Lambdacorporation/Seminarni_prace_Dvorak_2023/src/obrázky/500x500 bez můstků-1_1.jpg

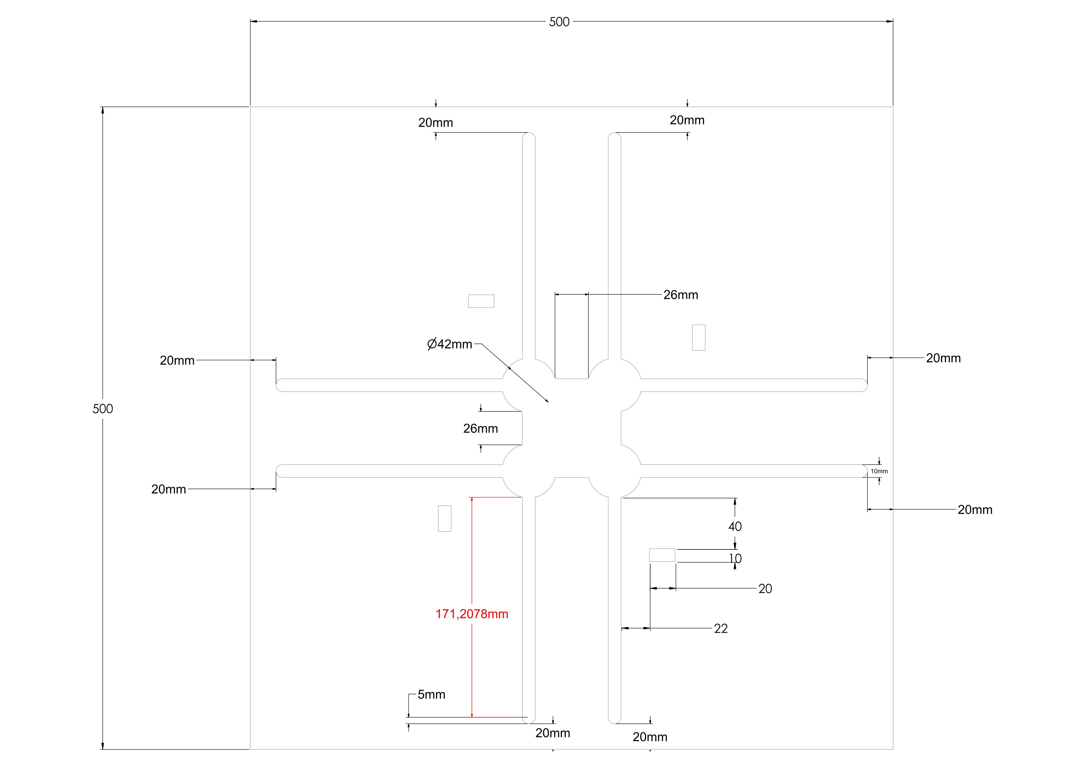
src/obrázky/500x500 bez můstků-1_1.jpg
