Lambdacorporation/Seminarni_prace_Dvorak_2023/src/obrázky/500x500 výpalek + zbytky.jpg

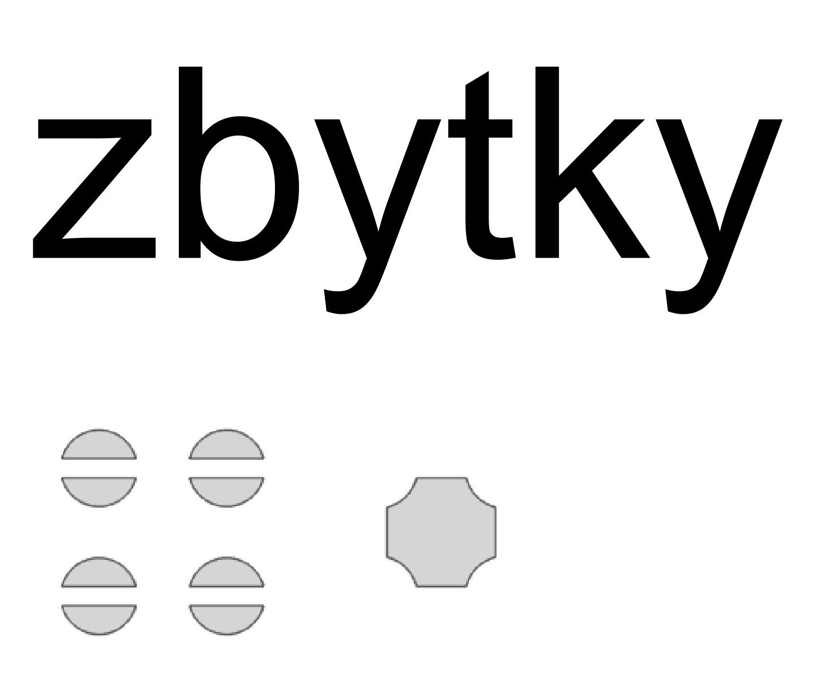
src/obrázky/500x500 výpalek + zbytky.jpg
