Lambdacorporation/Seminarni_prace_Dvorak_2023/src/obrázky/500x500 výpalek + zbytky_1.jpg

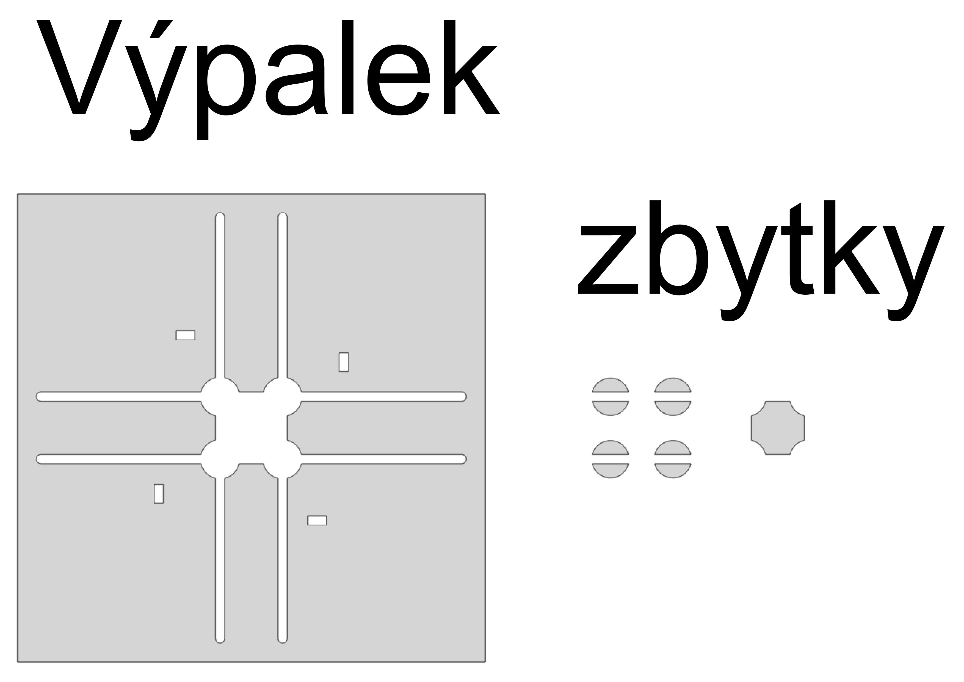
src/obrázky/500x500 výpalek + zbytky_1.jpg
