Lambdacorporation/Seminarni_prace_Dvorak_2023/src/obrázky/bok.png

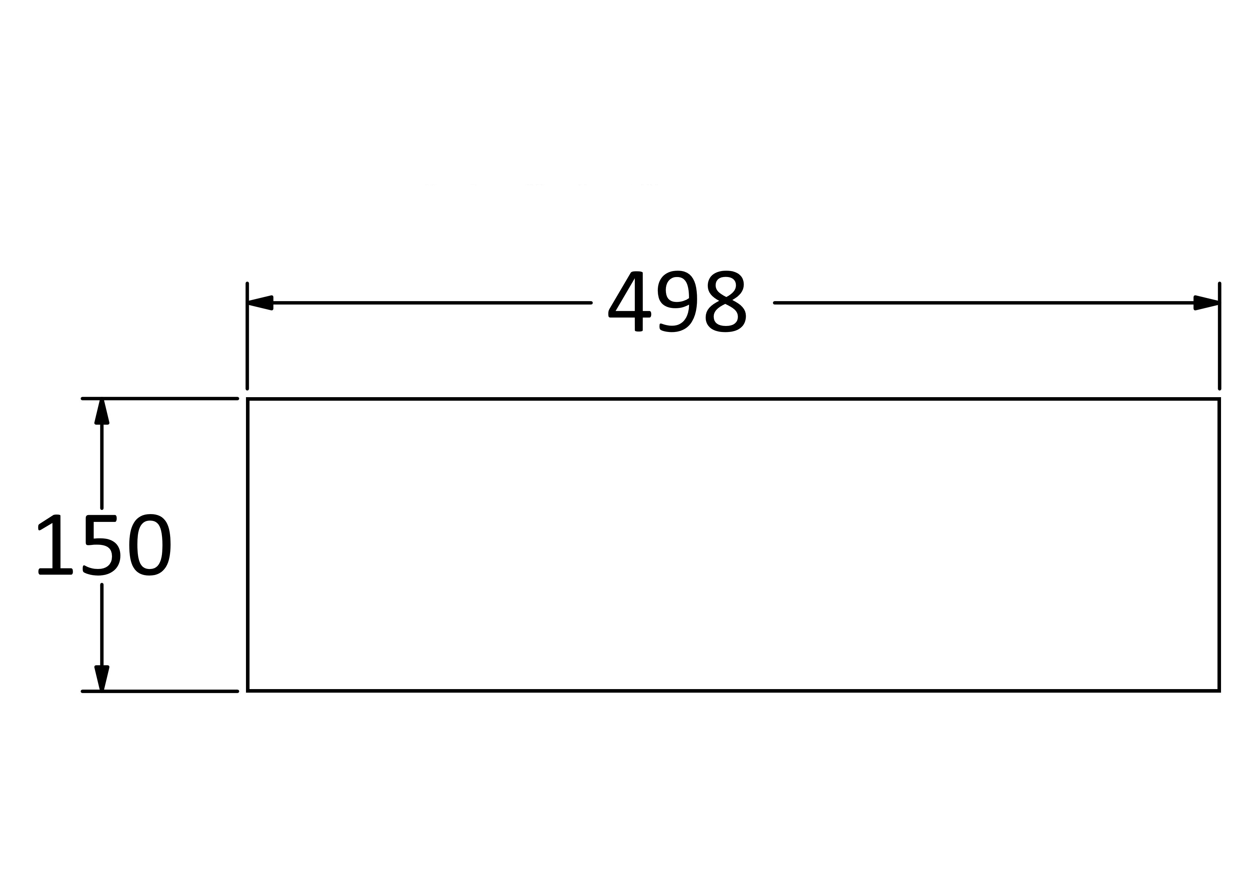
src/obrázky/bok.png
