Lambdacorporation/Seminarni_prace_Dvorak_2023/src/obrázky/boční stěna 2x_1.jpg

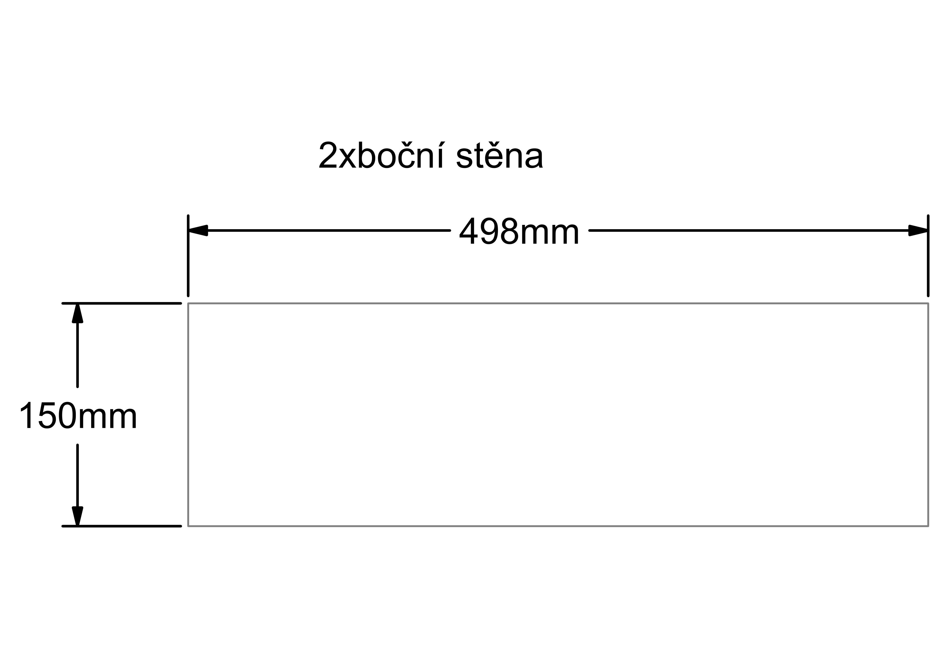
src/obrázky/boční stěna 2x_1.jpg
