Lambdacorporation/Seminarni_prace_Dvorak_2023/src/obrázky/dno 1x_1.jpg

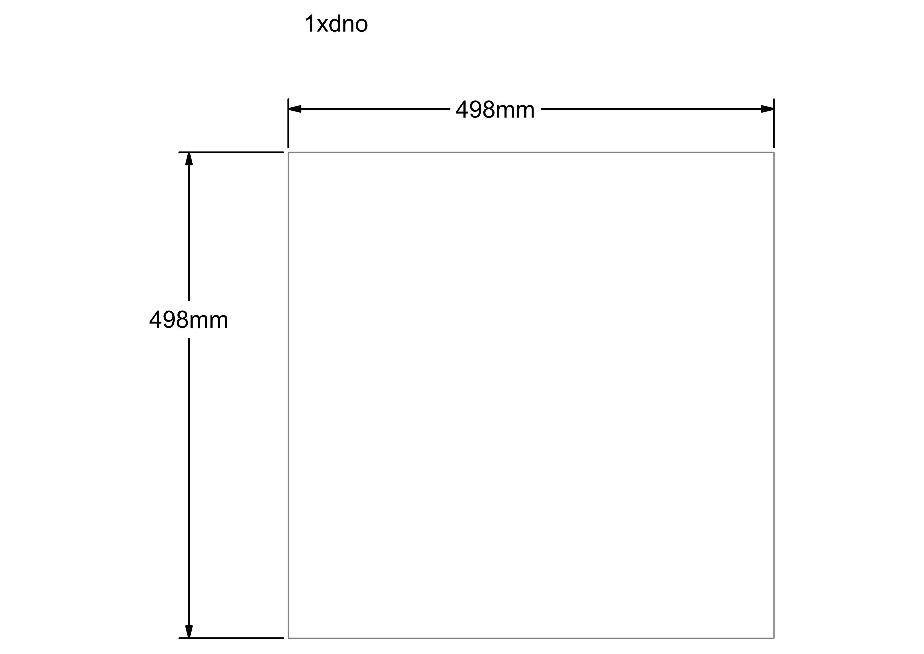
src/obrázky/dno 1x_1.jpg
