Lambdacorporation/Seminarni_prace_Dvorak_2023/src/obrázky/dno.png

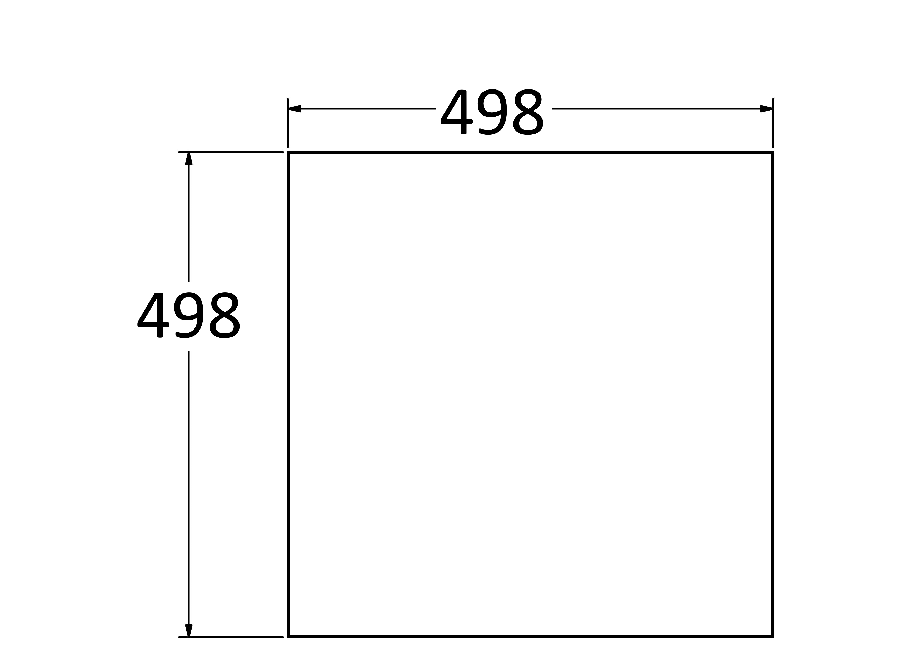
src/obrázky/dno.png
