Lambdacorporation/Seminarni_prace_Dvorak_2023/src/obrázky/krizovatky/dpv.bmp

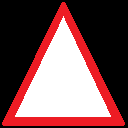
src/obrázky/krizovatky/dpv.bmp
