Lambdacorporation/Seminarni_prace_Dvorak_2023/src/obrázky/krizovatky/hpk.bmp

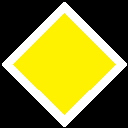
src/obrázky/krizovatky/hpk.bmp
