Lambdacorporation/Seminarni_prace_Dvorak_2023/src/obrázky/krizovatky/krizovatka6.jpg

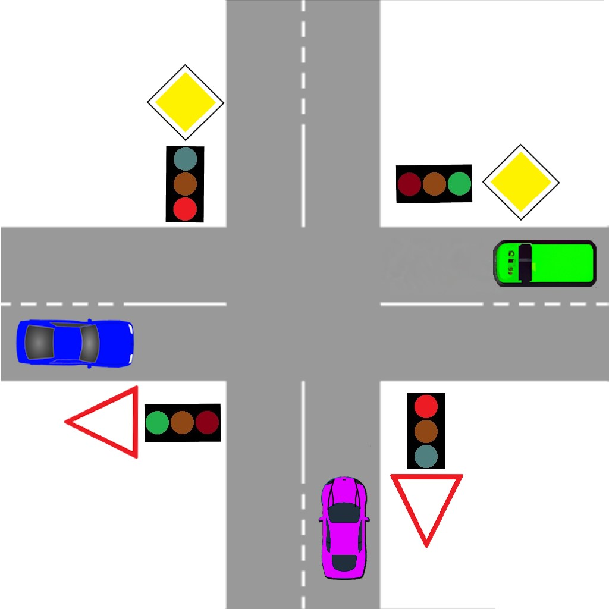
src/obrázky/krizovatky/krizovatka6.jpg
