Lambdacorporation/Seminarni_prace_Dvorak_2023/src/obrázky/krizovatky/krizovatka.png

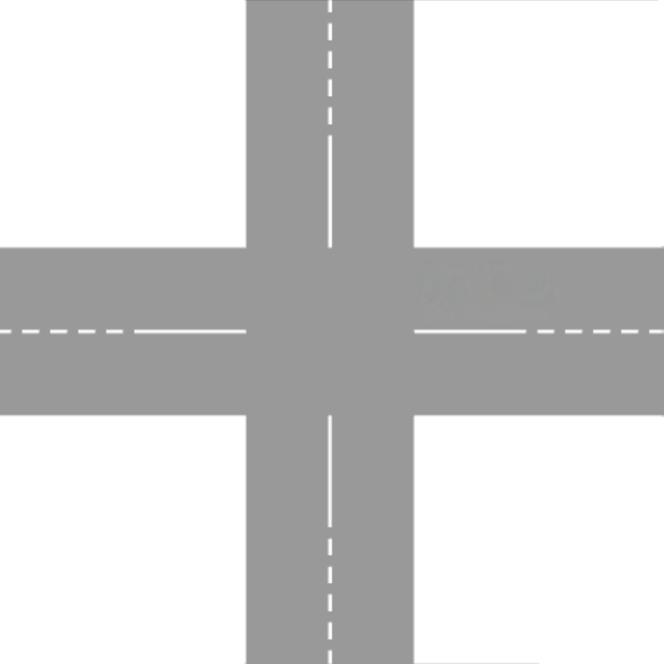
src/obrázky/krizovatky/krizovatka.png
