Lambdacorporation/Seminarni_prace_Dvorak_2023/src/obrázky/krizovatky/modre_auto.png

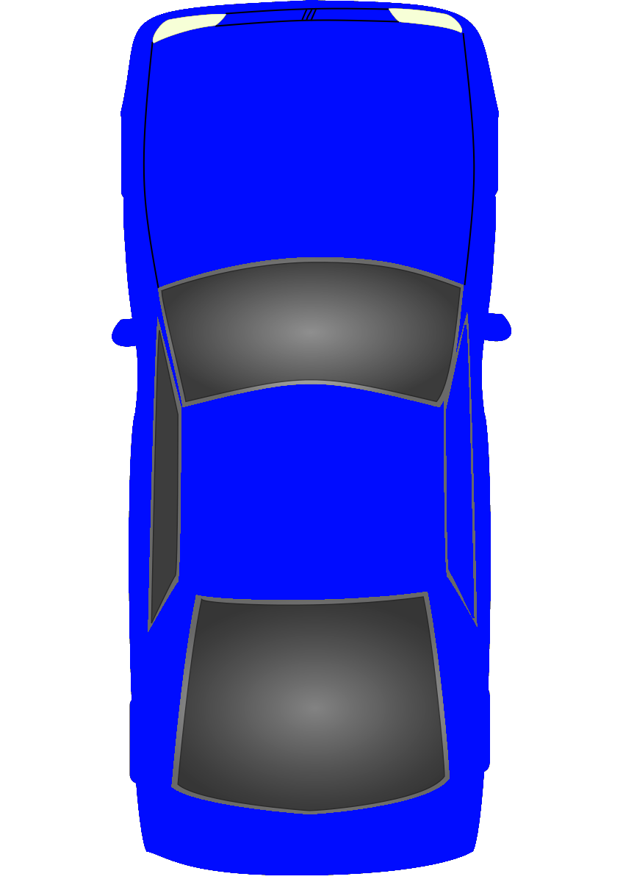
src/obrázky/krizovatky/modre_auto.png
