Lambdacorporation/Seminarni_prace_Dvorak_2023/src/obrázky/krizovatky/stop.png

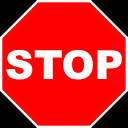
src/obrázky/krizovatky/stop.png
