Lambdacorporation/Seminarni_prace_Dvorak_2023/src/obrázky/předek.png

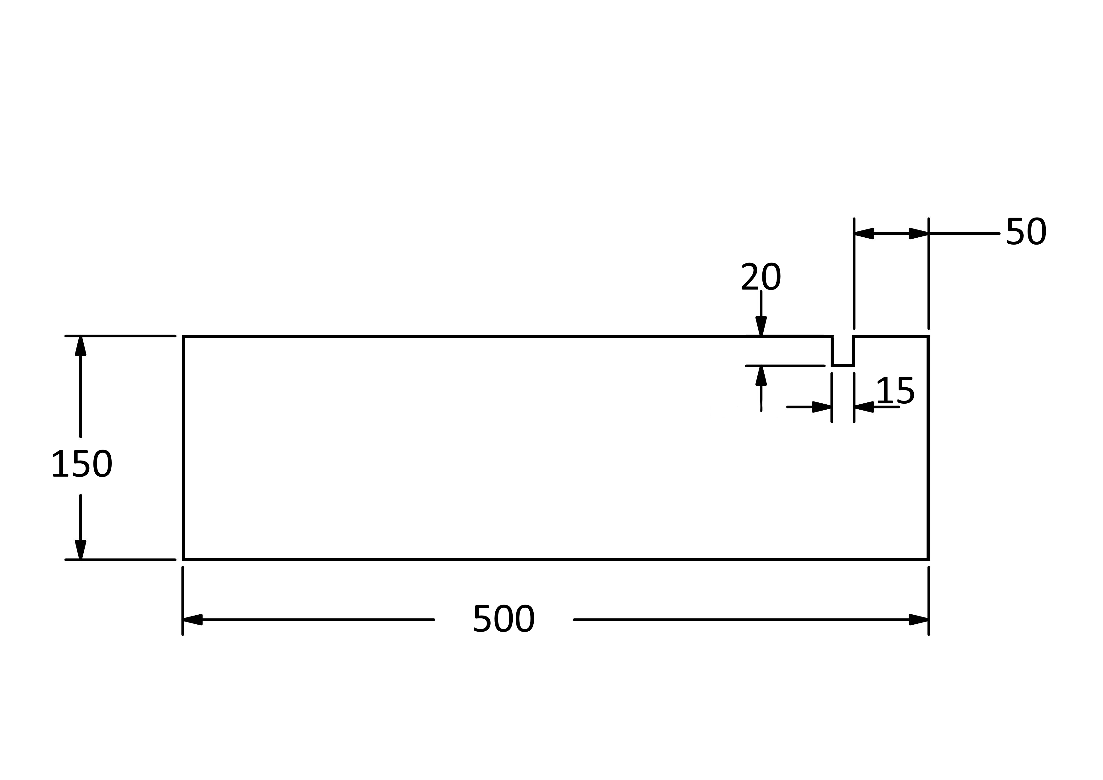
src/obrázky/předek.png
