Lambdacorporation/Seminarni_prace_Dvorak_2023/src/obrázky/přední stěna 1x_1.jpg

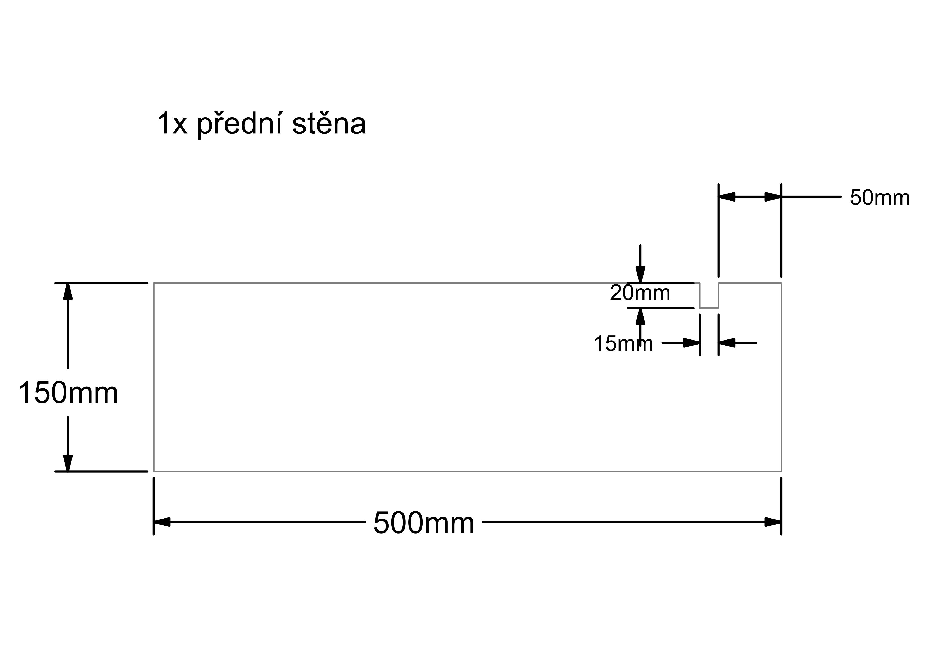
src/obrázky/přední stěna 1x_1.jpg
