Lambdacorporation/Seminarni_prace_Dvorak_2023/src/obrázky/screen_main.png

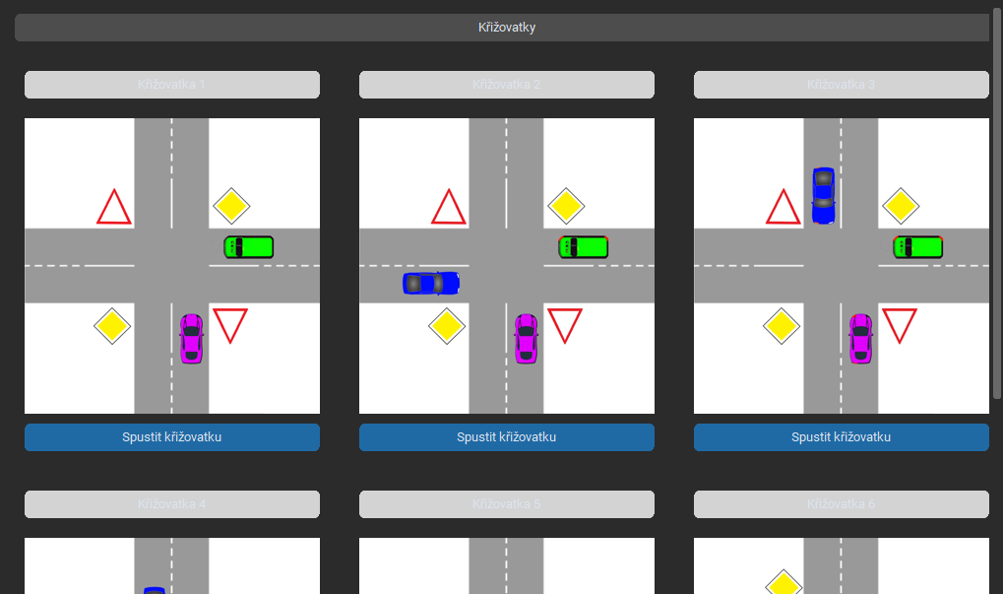
src/obrázky/screen_main.png
