Lambdacorporation/Seminarni_prace_Dvorak_2023/src/obrázky/viko.jpg

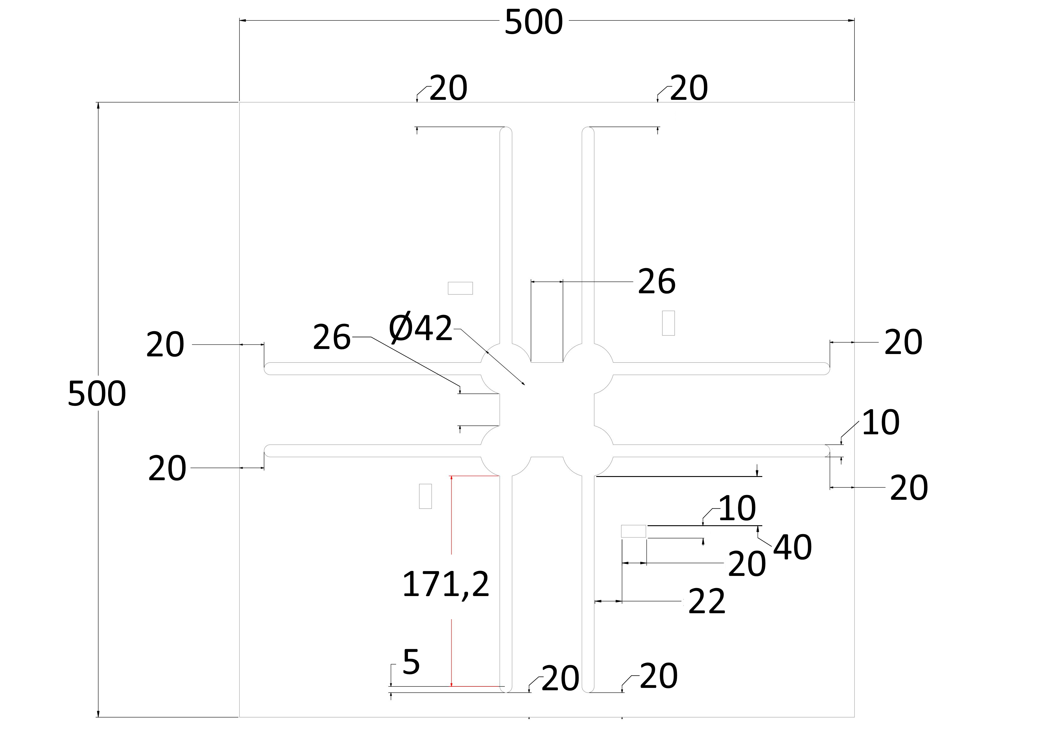
src/obrázky/viko.jpg
