Lambdacorporation/Seminarni_prace_Dvorak_2023/src/obrázky/zadní stěna 1x_1.jpg

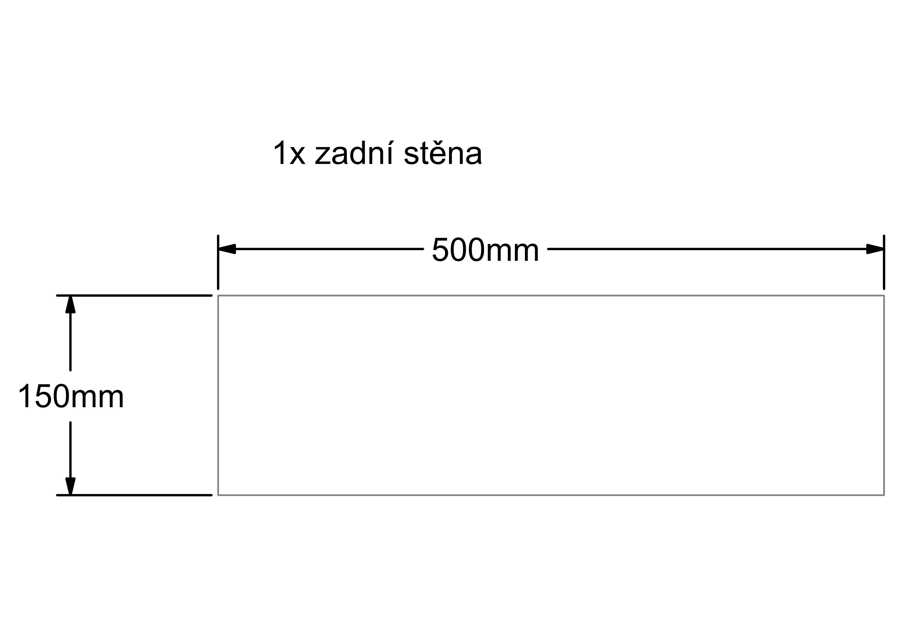
src/obrázky/zadní stěna 1x_1.jpg
