Lambdacorporation/Seminarni_prace_Dvorak_2023/src/modely/motor_add.stl

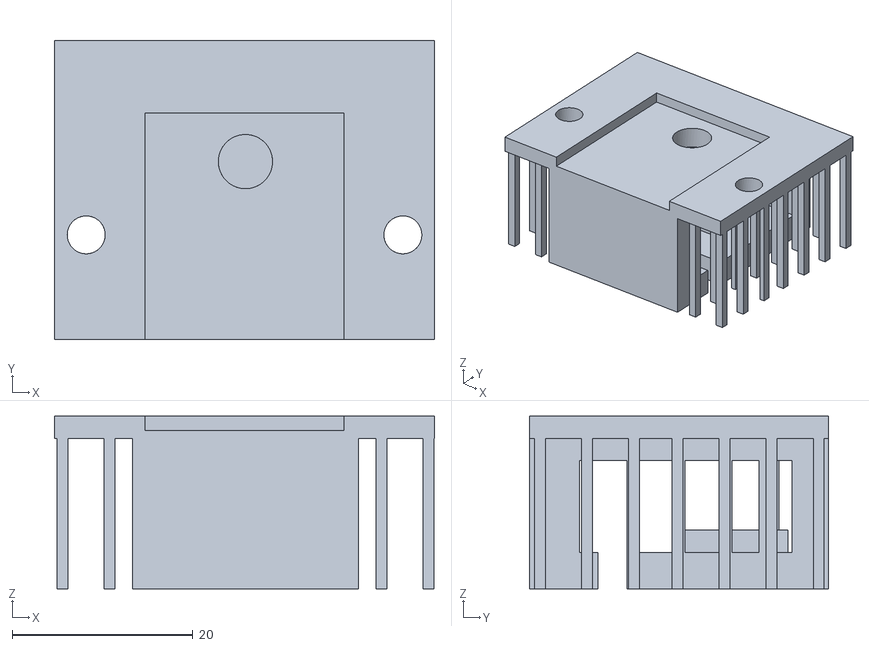
[picture p47: CAD file, 2024-03-03]
src/modely/motor_add.stl
42.0 x 33.0 x 19.1
